le-studio-5/MachineInfernale/ArduinoTeensyCodes/ColorPalette/ColorPalette.ino

#include <FastLED.h>

#define LED_PIN     0
#define NUM_LEDS    1
#define BRIGHTNESS  64
#define LED_TYPE    WS2812
#define COLOR_ORDER GRB
CRGB leds[NUM_LEDS];

#define UPDATES_PER_SECOND 100

CRGBPalette16 currentPalette;
TBlendType    currentBlending;

extern CRGBPalette16 myRedWhiteBluePalette;
extern const TProgmemPalette16 myRedWhiteBluePalette_p PROGMEM;


void setup() {
    delay( 3000 ); // power-up safety delay
    FastLED.addLeds<LED_TYPE, LED_PIN, COLOR_ORDER>(leds, NUM_LEDS).setCorrection( TypicalLEDStrip );
    FastLED.setBrightness(  BRIGHTNESS );
    
    currentPalette = RainbowColors_p;
    currentBlending = LINEARBLEND;
}


void loop()
{
    leds[0]= CHSV( random8(), 255, 128);
    
    FastLED.show();
    FastLED.delay(500);
}
